cjheath/hackrf/docs/images/rf_shield_5.jpg

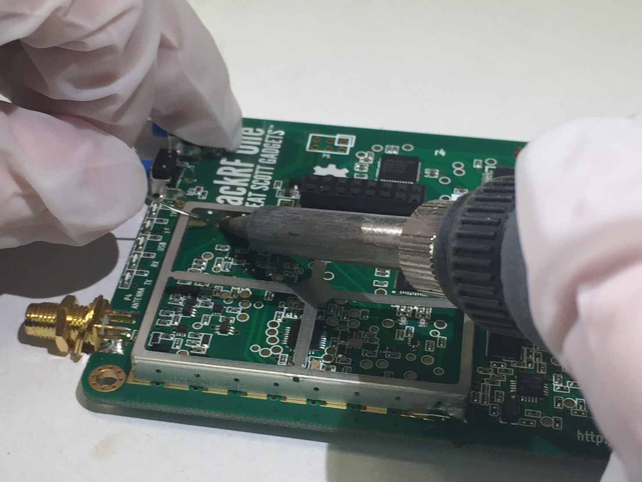
docs/images/rf_shield_5.jpg
