cjheath/hackrf/docs/images/rf_shield_6.jpg

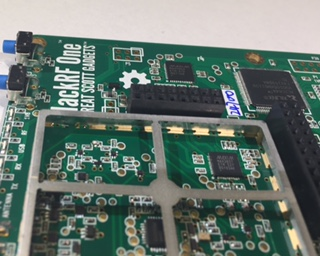
docs/images/rf_shield_6.jpg
