cjheath/hackrf/firmware/common/si5351c.c

/*
 * Copyright 2012-2022 Great Scott Gadgets <info@greatscottgadgets.com>
 * Copyright 2012 Jared Boone <jared@sharebrained.com>
 *
 * This file is part of HackRF.
 *
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
 * You should have received a copy of the GNU General Public License
 * along with this program; see the file COPYING.  If not, write to
 * the Free Software Foundation, Inc., 51 Franklin Street,
 * Boston, MA 02110-1301, USA.
 */

#include "si5351c.h"
#include "clkin.h"
#include "platform_detect.h"
#include "gpio_lpc.h"
#include "hackrf_core.h"
#include <libopencm3/lpc43xx/scu.h>

/* HackRF One r9 clock control */
// clang-format off
static struct gpio_t gpio_h1r9_clkin_en   = GPIO(5, 15);
static struct gpio_t gpio_h1r9_clkout_en  = GPIO(0,  9);
static struct gpio_t gpio_h1r9_mcu_clk_en = GPIO(0,  8);
// clang-format on

#include <stdbool.h>

static enum pll_sources active_clock_source = PLL_SOURCE_UNINITIALIZED;
/* External clock output default is deactivated as it creates noise */
static bool clkout_enabled = false;

/* write to single register */
void si5351c_write_single(si5351c_driver_t* const drv, uint8_t reg, uint8_t val)
{
	const uint8_t data_tx[] = {reg, val};
	si5351c_write(drv, data_tx, 2);
}

/* read single register */
uint8_t si5351c_read_single(si5351c_driver_t* const drv, uint8_t reg)
{
	const uint8_t data_tx[] = {reg};
	uint8_t data_rx[] = {0x00};
	i2c_bus_transfer(drv->bus, drv->i2c_address, data_tx, 1, data_rx, 1);
	return data_rx[0];
}

/*
 * Write to one or more contiguous registers. data[0] should be the first
 * register number, one or more values follow.
 */
void si5351c_write(
	si5351c_driver_t* const drv,
	const uint8_t* const data,
	const size_t data_count)
{
	i2c_bus_transfer(drv->bus, drv->i2c_address, data, data_count, NULL, 0);
}

/* Disable all CLKx outputs. */
void si5351c_disable_all_outputs(si5351c_driver_t* const drv)
{
	uint8_t data[] = {3, 0xFF};
	si5351c_write(drv, data, sizeof(data));
}

/* Turn off OEB pin control for all CLKx */
void si5351c_disable_oeb_pin_control(si5351c_driver_t* const drv)
{
	uint8_t data[] = {9, 0xFF};
	si5351c_write(drv, data, sizeof(data));
}

/* Power down all CLKx */
void si5351c_power_down_all_clocks(si5351c_driver_t* const drv)
{
	uint8_t data[] = {
		16,
		SI5351C_CLK_POWERDOWN,
		SI5351C_CLK_POWERDOWN,
		SI5351C_CLK_POWERDOWN,
		SI5351C_CLK_POWERDOWN,
		SI5351C_CLK_POWERDOWN,
		SI5351C_CLK_POWERDOWN,
		SI5351C_CLK_POWERDOWN | SI5351C_CLK_INT_MODE,
		SI5351C_CLK_POWERDOWN | SI5351C_CLK_INT_MODE};
	si5351c_write(drv, data, sizeof(data));
}

/*
 * Register 183: Crystal Internal Load Capacitance
 * Reads as 0xE4 on power-up
 * Set to 8pF based on crystal specs and HackRF One testing
 */
void si5351c_set_crystal_configuration(si5351c_driver_t* const drv)
{
	uint8_t data[] = {183, 0x80};
	si5351c_write(drv, data, sizeof(data));
}

/*
 * Register 187: Fanout Enable
 * Turn on XO and MultiSynth fanout only.
 */
void si5351c_enable_xo_and_ms_fanout(si5351c_driver_t* const drv)
{
	uint8_t data[] = {187, 0xD0};
	si5351c_write(drv, data, sizeof(data));
}

/*
 * Register 15: PLL Input Source
 * CLKIN_DIV=0 (Divide by 1)
 * PLLA_SRC=0 (XTAL)
 * PLLB_SRC=1 (CLKIN)
 */
void si5351c_configure_pll_sources(si5351c_driver_t* const drv)
{
	uint8_t data[] = {15, 0x08};

	si5351c_write(drv, data, sizeof(data));
}

/* MultiSynth NA (PLLA) and NB (PLLB) */
void si5351c_configure_pll_multisynth(si5351c_driver_t* const drv)
{
	/*PLLA: 25MHz XTAL * (0x0e00+512)/128 = 800mhz -> int mode */
	uint8_t data[] = {26, 0x00, 0x01, 0x00, 0x0E, 0x00, 0x00, 0x00, 0x00};
	si5351c_write(drv, data, sizeof(data));

	/*PLLB: 10MHz CLKIN * (0x2600+512)/128 = 800mhz */
	data[0] = 34;
	data[4] = 0x26;
	si5351c_write(drv, data, sizeof(data));
}

void si5351c_reset_pll(si5351c_driver_t* const drv)
{
	/* reset PLLA and PLLB */
	uint8_t data[] = {177, 0xA0};
	si5351c_write(drv, data, sizeof(data));
}

void si5351c_configure_multisynth(
	si5351c_driver_t* const drv,
	const uint_fast8_t ms_number,
	const uint32_t p1,
	const uint32_t p2,
	const uint32_t p3,
	const uint_fast8_t r_div)
{
	/*
	 * TODO: Check for p3 > 0? 0 has no meaning in fractional mode?
	 * And it makes for more jitter in integer mode.
	 */
	/*
	 * r is the r divider value encoded:
	 *   0 means divide by 1
	 *   1 means divide by 2
	 *   2 means divide by 4
	 *   ...
	 *   7 means divide by 128
	 */
	const uint_fast8_t register_number = 42 + (ms_number * 8);
	uint8_t data[] = {
		register_number,
		(p3 >> 8) & 0xFF,
		(p3 >> 0) & 0xFF,
		(r_div << 4) | (0 << 2) | ((p1 >> 16) & 0x3),
		(p1 >> 8) & 0xFF,
		(p1 >> 0) & 0xFF,
		(((p3 >> 16) & 0xF) << 4) | (((p2 >> 16) & 0xF) << 0),
		(p2 >> 8) & 0xFF,
		(p2 >> 0) & 0xFF};
	si5351c_write(drv, data, sizeof(data));
}

void si5351c_configure_clock_control(
	si5351c_driver_t* const drv,
	const enum pll_sources source)
{
	uint8_t pll;
	uint8_t clkout_ctrl;

#ifdef RAD1O
	(void) source;
	/* PLLA on XTAL */
	pll = SI5351C_CLK_PLL_SRC_A;
#endif

#if (defined JAWBREAKER || defined HACKRF_ONE)
	if (source == PLL_SOURCE_CLKIN) {
		/* PLLB on CLKIN */
		pll = SI5351C_CLK_PLL_SRC_B;
		if (detected_platform() == BOARD_ID_HACKRF1_R9) {
			/*
			 * HackRF One r9 always uses PLL A on the XTAL input
			 * but externally switches that input to CLKIN.
			 */
			pll = SI5351C_CLK_PLL_SRC_A;
			gpio_set(&gpio_h1r9_clkin_en);
		}
	} else {
		/* PLLA on XTAL */
		pll = SI5351C_CLK_PLL_SRC_A;
		if (detected_platform() == BOARD_ID_HACKRF1_R9) {
			gpio_clear(&gpio_h1r9_clkin_en);
		}
	}
#endif
	if (clkout_enabled) {
		clkout_ctrl = SI5351C_CLK_INT_MODE | SI5351C_CLK_PLL_SRC(pll) |
			SI5351C_CLK_SRC(SI5351C_CLK_SRC_MULTISYNTH_SELF) |
			SI5351C_CLK_IDRV(SI5351C_CLK_IDRV_8MA);
	} else {
		clkout_ctrl = SI5351C_CLK_POWERDOWN | SI5351C_CLK_INT_MODE;
	}

	/* Clock to CPU is deactivated as it is not used and creates noise */
	/* External clock output is kept in current state */
	uint8_t data[] = {
		16,
		SI5351C_CLK_FRAC_MODE | SI5351C_CLK_PLL_SRC(pll) |
			SI5351C_CLK_SRC(SI5351C_CLK_SRC_MULTISYNTH_SELF) |
			SI5351C_CLK_IDRV(SI5351C_CLK_IDRV_8MA),
		SI5351C_CLK_INT_MODE | SI5351C_CLK_PLL_SRC(pll) |
			SI5351C_CLK_SRC(SI5351C_CLK_SRC_MULTISYNTH_0_4) |
			SI5351C_CLK_IDRV(SI5351C_CLK_IDRV_2MA) | SI5351C_CLK_INV,
		SI5351C_CLK_INT_MODE | SI5351C_CLK_PLL_SRC(pll) |
			SI5351C_CLK_SRC(SI5351C_CLK_SRC_MULTISYNTH_0_4) |
			SI5351C_CLK_IDRV(SI5351C_CLK_IDRV_2MA),
		clkout_ctrl,
		SI5351C_CLK_INT_MODE | SI5351C_CLK_PLL_SRC(pll) |
			SI5351C_CLK_SRC(SI5351C_CLK_SRC_MULTISYNTH_SELF) |
			SI5351C_CLK_IDRV(SI5351C_CLK_IDRV_6MA) | SI5351C_CLK_INV,
		SI5351C_CLK_INT_MODE | SI5351C_CLK_PLL_SRC(pll) |
			SI5351C_CLK_SRC(SI5351C_CLK_SRC_MULTISYNTH_SELF) |
			SI5351C_CLK_IDRV(SI5351C_CLK_IDRV_4MA),
		SI5351C_CLK_POWERDOWN |
			SI5351C_CLK_INT_MODE, /* not connected, but: PLL A int mode */
		SI5351C_CLK_POWERDOWN |
			SI5351C_CLK_INT_MODE /* not connected, but: PLL B int mode */
	};
	if (detected_platform() == BOARD_ID_HACKRF1_R9) {
		data[1] = SI5351C_CLK_INT_MODE | SI5351C_CLK_PLL_SRC_A |
			SI5351C_CLK_SRC(SI5351C_CLK_SRC_MULTISYNTH_SELF) |
			SI5351C_CLK_IDRV(SI5351C_CLK_IDRV_6MA);
		data[2] = SI5351C_CLK_FRAC_MODE | SI5351C_CLK_PLL_SRC_A |
			SI5351C_CLK_SRC(SI5351C_CLK_SRC_MULTISYNTH_SELF) |
			SI5351C_CLK_IDRV(SI5351C_CLK_IDRV_4MA);
		data[3] = clkout_ctrl;
		data[4] = SI5351C_CLK_POWERDOWN;
		data[5] = SI5351C_CLK_POWERDOWN;
		data[6] = SI5351C_CLK_POWERDOWN;
	}
	si5351c_write(drv, data, sizeof(data));
}

#define SI5351C_CLK_ENABLE(x)  (0 << x)
#define SI5351C_CLK_DISABLE(x) (1 << x)
#define SI5351C_REG_OUTPUT_EN  (3)

void si5351c_enable_clock_outputs(si5351c_driver_t* const drv)
{
	/* Enable CLK outputs 0, 1, 2, 4, 5 only. */
	/* 7: Clock to CPU is deactivated as it is not used and creates noise */
	/* 3: External clock output is deactivated by default */
	uint8_t value = SI5351C_CLK_ENABLE(0) | SI5351C_CLK_ENABLE(1) |
		SI5351C_CLK_ENABLE(2) | SI5351C_CLK_ENABLE(4) | SI5351C_CLK_ENABLE(5) |
		SI5351C_CLK_DISABLE(6) | SI5351C_CLK_DISABLE(7);
	uint8_t clkout = 3;

	/* HackRF One r9 has only three clock generator outputs. */
	if (detected_platform() == BOARD_ID_HACKRF1_R9) {
		clkout = 2;
		value = SI5351C_CLK_ENABLE(0) | SI5351C_CLK_ENABLE(1) |
			SI5351C_CLK_DISABLE(3) | SI5351C_CLK_DISABLE(4) |
			SI5351C_CLK_DISABLE(5) | SI5351C_CLK_DISABLE(6) |
			SI5351C_CLK_DISABLE(7);
	}

	value |= (clkout_enabled) ? SI5351C_CLK_ENABLE(clkout) :
				    SI5351C_CLK_DISABLE(clkout);
	uint8_t data[] = {SI5351C_REG_OUTPUT_EN, value};
	si5351c_write(drv, data, sizeof(data));

	if ((clkout_enabled) && (detected_platform() == BOARD_ID_HACKRF1_R9)) {
		gpio_set(&gpio_h1r9_clkout_en);
	} else {
		gpio_clear(&gpio_h1r9_clkout_en);
	}
}

void si5351c_set_int_mode(
	si5351c_driver_t* const drv,
	const uint_fast8_t ms_number,
	const uint_fast8_t on)
{
	uint8_t data[] = {16, 0};

	if (ms_number < 8) {
		data[0] = 16 + ms_number;
		data[1] = si5351c_read_single(drv, data[0]);

		if (on) {
			data[1] |= SI5351C_CLK_INT_MODE;
		} else {
			data[1] &= ~(SI5351C_CLK_INT_MODE);
		}

		si5351c_write(drv, data, 2);
	}
}

void si5351c_set_clock_source(si5351c_driver_t* const drv, const enum pll_sources source)
{
	if (source == active_clock_source) {
		return;
	}
	si5351c_configure_clock_control(drv, source);
	active_clock_source = source;
	if (detected_platform() == BOARD_ID_HACKRF1_R9) {
		/* 25MHz XTAL * (0x0e00+512)/128 = 800mhz -> int mode */
		uint8_t pll_data[] = {26, 0x00, 0x01, 0x00, 0x0E, 0x00, 0x00, 0x00, 0x00};
		if (source == PLL_SOURCE_CLKIN) {
			/* 10MHz CLKIN * (0x2600+512)/128 = 800mhz */
			pll_data[4] = 0x26;
		}
		si5351c_write(drv, pll_data, sizeof(pll_data));
		si5351c_reset_pll(drv);
	}
}

bool si5351c_clkin_signal_valid(si5351c_driver_t* const drv)
{
	if (detected_platform() == BOARD_ID_HACKRF1_R9) {
		uint32_t f = clkin_frequency();
		return (f > 9000000) && (f < 11000000);
	} else {
		return (si5351c_read_single(drv, 0) & SI5351C_LOS) == 0;
	}
}

void si5351c_clkout_enable(si5351c_driver_t* const drv, uint8_t enable)
{
	clkout_enabled = (enable > 0);

	//FIXME this should be somewhere else
	uint8_t clkout = 3;
	/* HackRF One r9 has only three clock generator outputs. */
	if (detected_platform() == BOARD_ID_HACKRF1_R9) {
		clkout = 2;
	}
	/* Configure clock to 10MHz */
	si5351c_configure_multisynth(drv, clkout, 80 * 128 - 512, 0, 1, 0);

	si5351c_configure_clock_control(drv, active_clock_source);
	si5351c_enable_clock_outputs(drv);
}

void si5351c_init(si5351c_driver_t* const drv)
{
	if (detected_platform() == BOARD_ID_HACKRF1_R9) {
		/* CLKIN_EN */
		scu_pinmux(SCU_H1R9_CLKIN_EN, SCU_GPIO_FAST | SCU_CONF_FUNCTION4);
		gpio_clear(&gpio_h1r9_clkin_en);
		gpio_output(&gpio_h1r9_clkin_en);

		/* CLKOUT_EN */
		scu_pinmux(SCU_H1R9_CLKOUT_EN, SCU_GPIO_FAST | SCU_CONF_FUNCTION0);
		gpio_clear(&gpio_h1r9_clkout_en);
		gpio_output(&gpio_h1r9_clkout_en);

		/* MCU_CLK_EN */
		scu_pinmux(SCU_H1R9_MCU_CLK_EN, SCU_GPIO_FAST | SCU_CONF_FUNCTION0);
		gpio_clear(&gpio_h1r9_mcu_clk_en);
		gpio_output(&gpio_h1r9_mcu_clk_en);
	}
	(void) drv;
}
