cjheath/hackrf/firmware/common/rad1o/smallfonts.c

/* Partially based on original code for the KS0108 by Stephane Rey */

/**************************************************************************/
/*! 
    @file     smallfonts.c
    @author   K. Townsend (microBuilder.eu)
    @date     22 March 2010
    @version  0.10

    @section LICENSE

    Software License Agreement (BSD License)

    Copyright (c) 2010, microBuilder SARL
    All rights reserved.

    Redistribution and use in source and binary forms, with or without
    modification, are permitted provided that the following conditions are met:
    1. Redistributions of source code must retain the above copyright
    notice, this list of conditions and the following disclaimer.
    2. Redistributions in binary form must reproduce the above copyright
    notice, this list of conditions and the following disclaimer in the
    documentation and/or other materials provided with the distribution.
    3. Neither the name of the copyright holders nor the
    names of its contributors may be used to endorse or promote products
    derived from this software without specific prior written permission.

    THIS SOFTWARE IS PROVIDED BY THE COPYRIGHT HOLDERS ''AS IS'' AND ANY
    EXPRESS OR IMPLIED WARRANTIES, INCLUDING, BUT NOT LIMITED TO, THE IMPLIED
    WARRANTIES OF MERCHANTABILITY AND FITNESS FOR A PARTICULAR PURPOSE ARE
    DISCLAIMED. IN NO EVENT SHALL THE COPYRIGHT HOLDER BE LIABLE FOR ANY
    DIRECT, INDIRECT, INCIDENTAL, SPECIAL, EXEMPLARY, OR CONSEQUENTIAL DAMAGES
    (INCLUDING, BUT NOT LIMITED TO, PROCUREMENT OF SUBSTITUTE GOODS OR SERVICES;
    LOSS OF USE, DATA, OR PROFITS; OR BUSINESS INTERRUPTION) HOWEVER CAUSED AND
    ON ANY THEORY OF LIABILITY, WHETHER IN CONTRACT, STRICT LIABILITY, OR TORT
    (INCLUDING NEGLIGENCE OR OTHERWISE) ARISING IN ANY WAY OUT OF THE USE OF THIS
    SOFTWARE, EVEN IF ADVISED OF THE POSSIBILITY OF SUCH DAMAGE.
*/
/**************************************************************************/
#include "smallfonts.h"

/* System 7x8 */
const uint8_t au8Font7x8[] = {
	0,   0,   0,   0,   0,   0,   0,   //' '
	0,   6,   95,  95,  6,   0,   0,   //'!'
	0,   7,   7,   0,   7,   7,   0,   //'"'
	20,  127, 127, 20,  127, 127, 20,  //'#'
	36,  46,  107, 107, 58,  18,  0,   //'$'
	70,  102, 48,  24,  12,  102, 98,  //'%'
	48,  122, 79,  93,  55,  122, 72,  //'&'
	4,   7,   3,   0,   0,   0,   0,   //'''
	0,   28,  62,  99,  65,  0,   0,   //'('
	0,   65,  99,  62,  28,  0,   0,   //')'
	8,   42,  62,  28,  28,  62,  42,  //'*'
	8,   8,   62,  62,  8,   8,   0,   //'+'
	0,   128, 224, 96,  0,   0,   0,   //','
	8,   8,   8,   8,   8,   8,   0,   //'-'
	0,   0,   96,  96,  0,   0,   0,   //'.'
	96,  48,  24,  12,  6,   3,   1,   //'/'
	62,  127, 113, 89,  77,  127, 62,  //'0'
	64,  66,  127, 127, 64,  64,  0,   //'1'
	98,  115, 89,  73,  111, 102, 0,   //'2'
	34,  99,  73,  73,  127, 54,  0,   //'3'
	24,  28,  22,  83,  127, 127, 80,  //'4'
	39,  103, 69,  69,  125, 57,  0,   //'5'
	60,  126, 75,  73,  121, 48,  0,   //'6'
	3,   3,   113, 121, 15,  7,   0,   //'7'
	54,  127, 73,  73,  127, 54,  0,   //'8'
	6,   79,  73,  105, 63,  30,  0,   //'9'
	0,   0,   102, 102, 0,   0,   0,   //':'
	0,   128, 230, 102, 0,   0,   0,   //';'
	8,   28,  54,  99,  65,  0,   0,   //'<'
	36,  36,  36,  36,  36,  36,  0,   //'='
	0,   65,  99,  54,  28,  8,   0,   //'>'
	2,   3,   81,  89,  15,  6,   0,   //'?'
	62,  127, 65,  93,  93,  31,  30,  //'@'
	124, 126, 19,  19,  126, 124, 0,   //'A'
	65,  127, 127, 73,  73,  127, 54,  //'B'
	28,  62,  99,  65,  65,  99,  34,  //'C'
	65,  127, 127, 65,  99,  62,  28,  //'D'
	65,  127, 127, 73,  93,  65,  99,  //'E'
	65,  127, 127, 73,  29,  1,   3,   //'F'
	28,  62,  99,  65,  81,  115, 114, //'G'
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
};

/* Global variables */
const struct FONT_DEF Font_7x8 = {7, 8, 32, 128, au8Font7x8, NULL, NULL};
