cjheath/hackrf/host/hackrf-tools/src/hackrf_spiflash.c

/*
 * Copyright 2012-2022 Great Scott Gadgets <info@greatscottgadgets.com>
 * Copyright 2012 Jared Boone <jared@sharebrained.com>
 * Copyright 2013 Benjamin Vernoux <titanmkd@gmail.com>
 *
 * This file is part of HackRF.
 *
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
 * You should have received a copy of the GNU General Public License
 * along with this program; see the file COPYING.  If not, write to
 * the Free Software Foundation, Inc., 51 Franklin Street,
 * Boston, MA 02110-1301, USA.
 */

#include <hackrf.h>

#include <stdio.h>
#include <stdlib.h>
#include <string.h>
#include <getopt.h>
#include <sys/types.h>

#ifndef bool
typedef int bool;
	#define true 1
	#define false 0
#endif

#ifdef _MSC_VER
	#ifdef _WIN64
typedef int64_t ssize_t;
	#else
typedef int32_t ssize_t;
	#endif
#endif

/* 8 Mbit flash */
#define MAX_LENGTH 0x100000

static struct option long_options[] = {
	{"address", required_argument, 0, 'a'},
	{"length", required_argument, 0, 'l'},
	{"read", required_argument, 0, 'r'},
	{"write", required_argument, 0, 'w'},
	{"compatibility", no_argument, 0, 'c'},
	{"device", required_argument, 0, 'd'},
	{"reset", no_argument, 0, 'R'},
	{"status", no_argument, 0, 's'},
	{"clear", no_argument, 0, 'c'},
	{"verbose", no_argument, 0, 'v'},
	{"help", no_argument, 0, 'h'},
	{0, 0, 0, 0},
};

/* Check for USB product string descriptor text in firmware file
 * It should match the appropriate one for the BOARD_ID
 * If you're already running firmware that reports the wrong ID
 * I can't help you, but you can use the -i optionto ignore (or DFU)
 */
int compatibility_check_og(uint8_t* data, int length, hackrf_device* device)
{
	int str_len, i, j;
	bool match = false;
	uint8_t board_id;
	char* dev_str;
	hackrf_board_id_read(device, &board_id);
	switch (board_id) {
	case BOARD_ID_JAWBREAKER:
		dev_str = "HackRF Jawbreaker";
		str_len = 17;
		break;
	case BOARD_ID_HACKRF1_OG:
		dev_str = "HackRF One";
		str_len = 10;
		break;
	case BOARD_ID_RAD1O:
		dev_str = "rad1o";
		str_len = 5;
		break;
	default:
		printf("Unsupported Board ID");
		return EXIT_FAILURE;
	}
	// Search for dev_str in uint8_t array of bytes that we're flashing
	for (i = 0; i < length - str_len; i++) {
		if (data[i] == dev_str[0]) {
			match = true;
			for (j = 1; j < str_len; j++) {
				if ((data[i + j * 2] != dev_str[j]) ||
				    (data[1 + i + j * 2] != 0x00)) {
					match = false;
					break;
				}
			}
			if (match) {
				return EXIT_SUCCESS;
			}
		}
	}
	return EXIT_FAILURE;
}

#define FW_INFO_LOCATION              0x400
#define FW_MAGIC_OFFSET               0
#define FW_STRUCT_VERSION_OFFSET      8
#define FW_SUPPORTED_PLATFORMS_OFFSET 12

#define FROM_LE32(x) ((x)[0] | ((x)[1] << 8) | ((x)[2] << 16) | ((x)[3] << 24))
#define FROM_LE16(x) ((x)[0] | ((x)[1] << 8))

int compatibility_check(uint8_t* data, int length, hackrf_device* device)
{
	uint8_t board_id;
	hackrf_board_id_read(device, &board_id);

	uint8_t* fw_info = data + FW_INFO_LOCATION;
	if (strncmp((char*) fw_info + FW_MAGIC_OFFSET, "HACKRFFW", 8) != 0) {
		// Couldn't find firmware info structure,
		// revert to old compatibility check method if possible.
		if (board_id != BOARD_ID_HACKRF1_R9) {
			return compatibility_check_og(data, length, device);
		}

		return EXIT_FAILURE;
	}

	uint32_t platform_required = hackrf_board_id_platform(board_id);
	if (platform_required == 0) {
		fprintf(stderr,
			"Could not find appropriate platform for board id %u (%s).\n",
			board_id,
			hackrf_board_id_name(board_id));
		return EXIT_FAILURE;
	}

	uint32_t struct_version = FROM_LE16(fw_info + FW_STRUCT_VERSION_OFFSET);
	if (struct_version == 1) {
		uint32_t supported_platforms =
			FROM_LE32(fw_info + FW_SUPPORTED_PLATFORMS_OFFSET);
		if (platform_required & supported_platforms) {
			return EXIT_SUCCESS;
		} else {
			return EXIT_FAILURE;
		}
	} else {
		fprintf(stderr,
			"Unrecognised firmware info structure version %u. This may require a newer hackrf_spiflash version.\n",
			struct_version);
		return EXIT_FAILURE;
	}
}

int parse_u32(char* s, uint32_t* const value)
{
	char* s_end;
	uint_fast8_t base = 10;
	uint32_t u32_value;

	if (strlen(s) > 2) {
		if (s[0] == '0') {
			if ((s[1] == 'x') || (s[1] == 'X')) {
				base = 16;
				s += 2;
			} else if ((s[1] == 'b') || (s[1] == 'B')) {
				base = 2;
				s += 2;
			}
		}
	}

	s_end = s;
	u32_value = strtoul(s, &s_end, base);
	if ((s != s_end) && (*s_end == 0)) {
		*value = u32_value;
		return HACKRF_SUCCESS;
	} else {
		return HACKRF_ERROR_INVALID_PARAM;
	}
}

static void usage()
{
	printf("Usage:\n");
	printf("\t-h, --help: this help\n");
	printf("\t-a, --address <n>: starting address (default: 0)\n");
	printf("\t-l, --length <n>: number of bytes to read (default: %d)\n", MAX_LENGTH);
	printf("\t-r, --read <filename>: Read data into file.\n");
	printf("\t-w, --write <filename>: Write data from file.\n");
	printf("\t-i, --no-check: Skip check for firmware compatibility with target device.\n");
	printf("\t-d, --device <serialnumber>: Serial number of device, if multiple devices\n");
	printf("\t-s, --status: Read SPI flash status registers before other operations.\n");
	printf("\t-c, --clear: Clear SPI flash status registers before other operations.\n");
	printf("\t-R, --reset: Reset HackRF after other operations.\n");
	printf("\t-v, --verbose: Verbose output.\n");
}
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
